VCHSRobots/Mag4Device/Mag4Software/Mag4Pico/pwm_reader/pwm4.cpp

#include <stdio.h>

#include "pico/stdlib.h"
#include "pico/time.h"

#include "PwmIn.h"

#define NUM_OF_PINS 4

int main()
{
    // needed for printf
    stdio_init_all();
    printf("PwmIn on 4 pins\n");

    // set PwmIn
    uint pin_list[NUM_OF_PINS] = {18, 19, 20, 21};
    PwmIn my_PwmIn(pin_list, NUM_OF_PINS);

    while (true)
    {
        // adviced empty (for now) function of sdk
        tight_loop_contents();

        // translate pwm of input to output
        float PW_0 = my_PwmIn.read_PW(0);
        float PW_1 = my_PwmIn.read_PW(1);
        float PW_2 = my_PwmIn.read_PW(2);
        float PW_3 = my_PwmIn.read_PW(3);
        printf("PW_0=%f PW_1=%f PW_2=%f PW_3=%f\n", PW_0, PW_1, PW_2, PW_3);
        sleep_ms(100);
    }
}
